nickthelegend/orchestrator-pad/firmware/orchestrator_pad/certs.h

#pragma once

// Root CA for HTTPS to a Tailscale Funnel URL (https://<machine>.<tailnet>.ts.net).
// Funnel serves a Let's Encrypt certificate, which chains to ISRG Root X1 — so
// pinning this one root lets the pad verify the server and refuse a MITM (which
// matters: the bearer token rides on this connection). Valid until 2035-06-04.
//
// Source: https://letsencrypt.org/certs/isrgrootx1.pem
// SHA-256: 96:BC:EC:06:26:49:76:F3:74:60:77:9A:CF:28:C5:A7:CF:E8:A3:C0:AA:E1:1A:8F:FC:EE:05:C0:BD:DF:08:C6
//
// Plain HTTP (a LAN IP like http://192.168.1.20:8080) doesn't touch this.
static const char ISRG_ROOT_X1[] = R"CERT(-----BEGIN CERTIFICATE-----
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
-----END CERTIFICATE-----
)CERT";
